csun/ellipsis_split_files/plates/v2/r_plate_FINAL.dxf

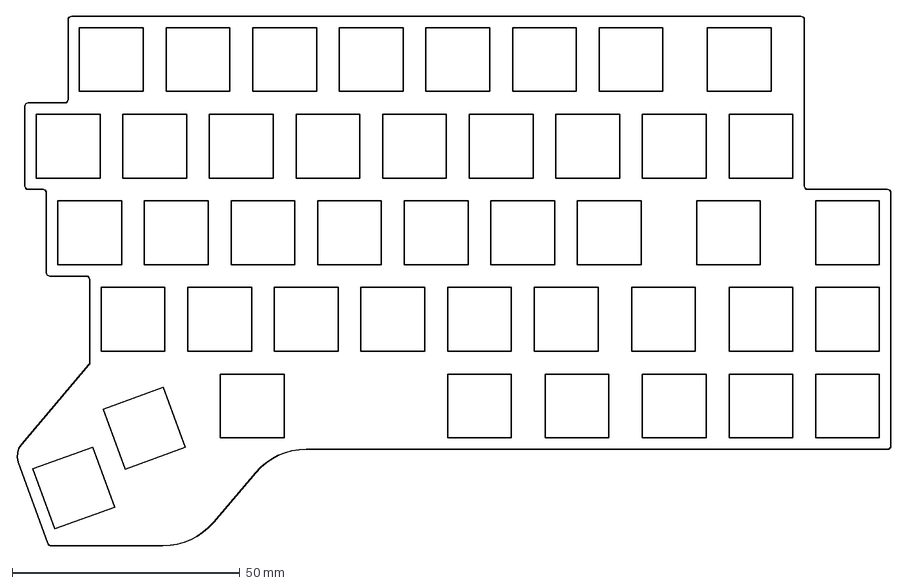
[picture p17: CAD file, 2023-03-02]
plates/v2/r_plate_FINAL.dxf
191.9 x 116.2 mm
